m0wmt/audio-guestbook/images/boards.jpeg

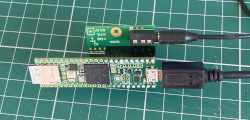
images/boards.jpeg
