m0wmt/audio-guestbook/images/cover-off.jpeg

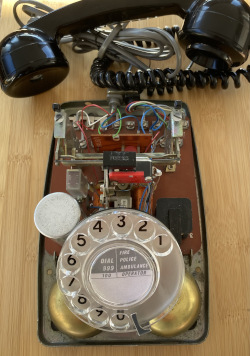
images/cover-off.jpeg
