m0wmt/audio-guestbook/images/press-button.jpeg

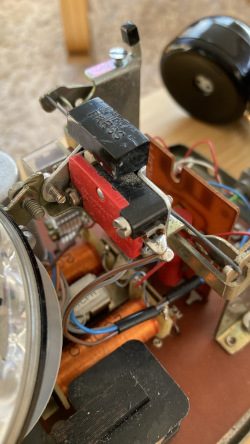
images/press-button.jpeg
