m0wmt/audio-guestbook/images/rocker-switch.jpeg

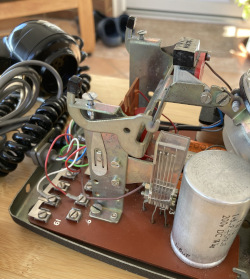
images/rocker-switch.jpeg
